CanBeLeftBlank/mk312-bt-chi/images/V1.4-chi/IMG_20220905_133640.jpg

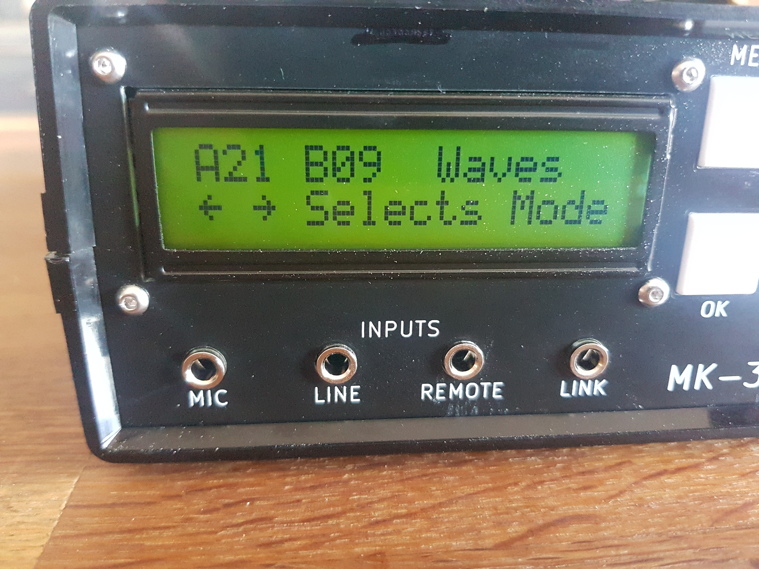
images/V1.4-chi/IMG_20220905_133640.jpg
